timville85/4dapter/Product Images/IMG_2103.jpeg

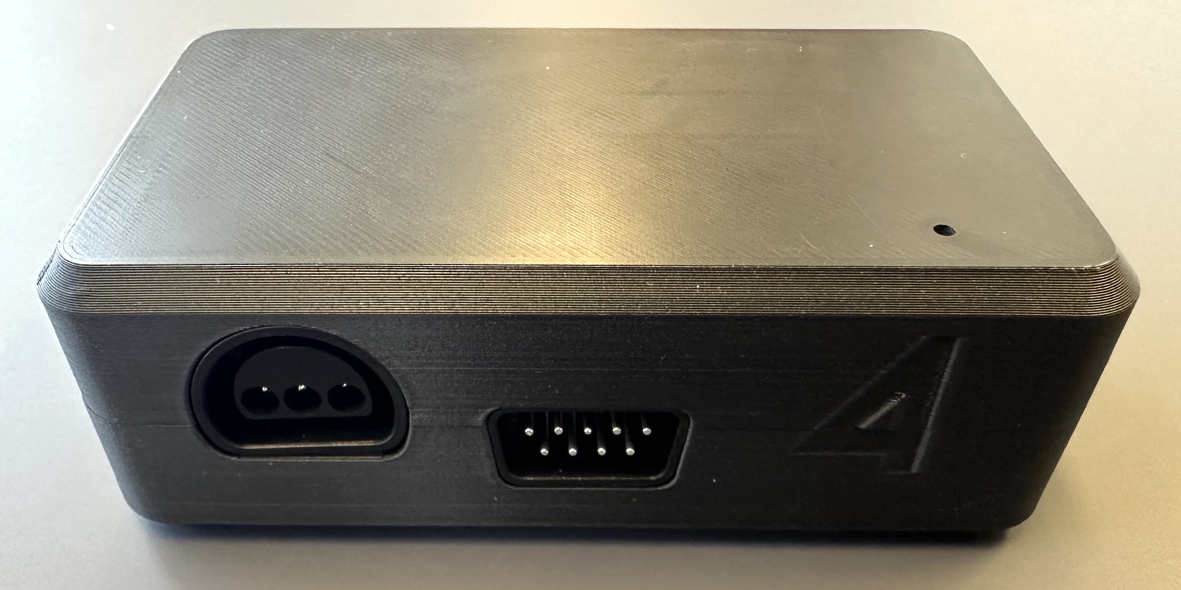
Product Images/IMG_2103.jpeg
