timville85/4dapter/Product Images/IMG_2104.jpeg

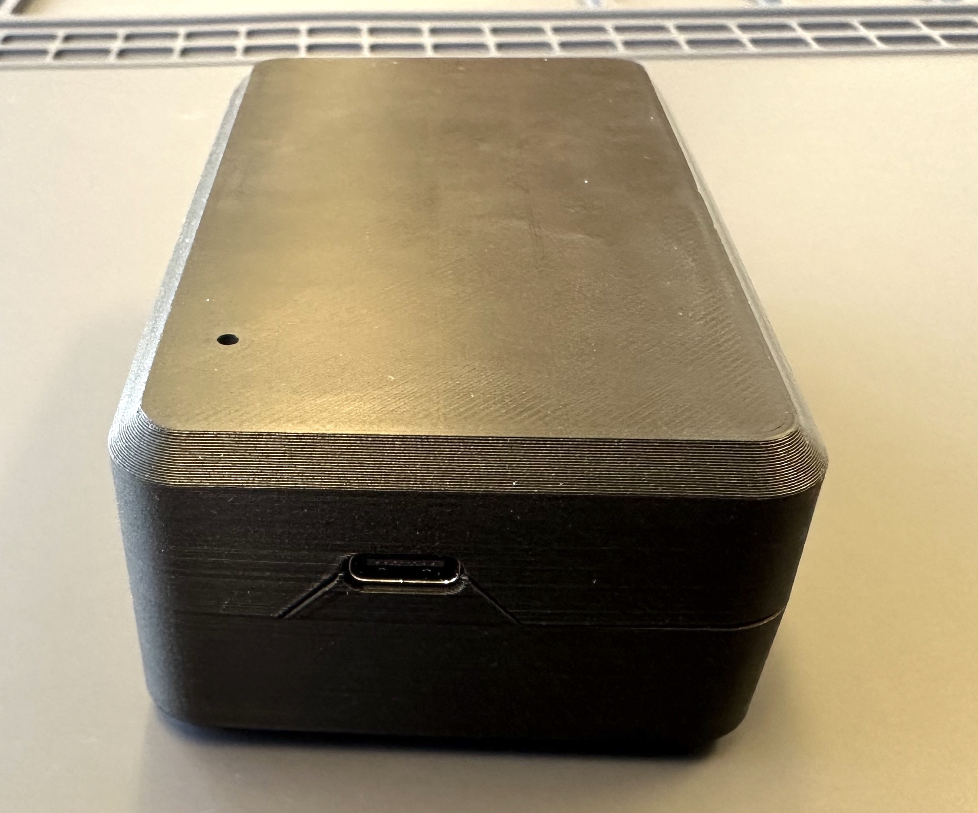
Product Images/IMG_2104.jpeg
