timville85/4dapter/Product Images/IMG_2105.jpeg

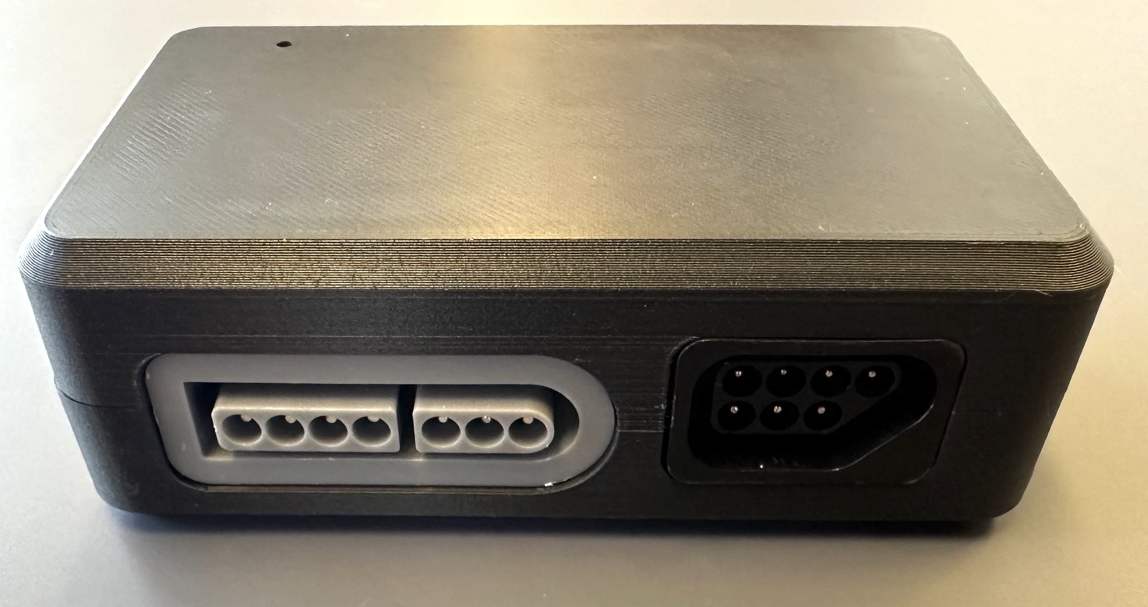
Product Images/IMG_2105.jpeg
