timville85/4dapter/Product Images/IMG_2106.jpeg

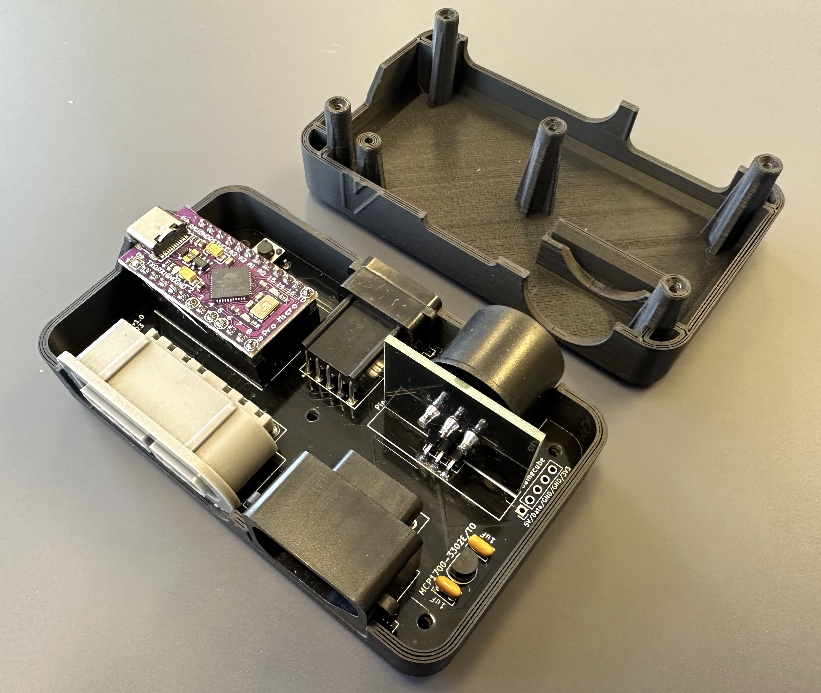
Product Images/IMG_2106.jpeg
