timville85/4dapter/Product Images/IMG_2107.jpeg

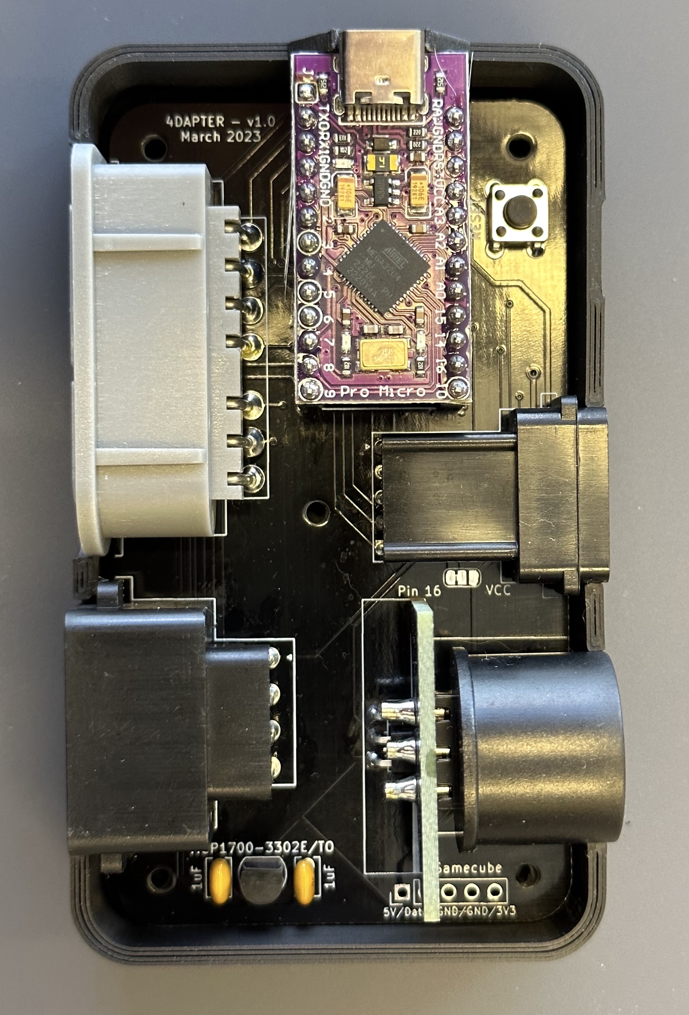
Product Images/IMG_2107.jpeg
