timville85/4dapter/Product Images/IMG_2108.jpeg

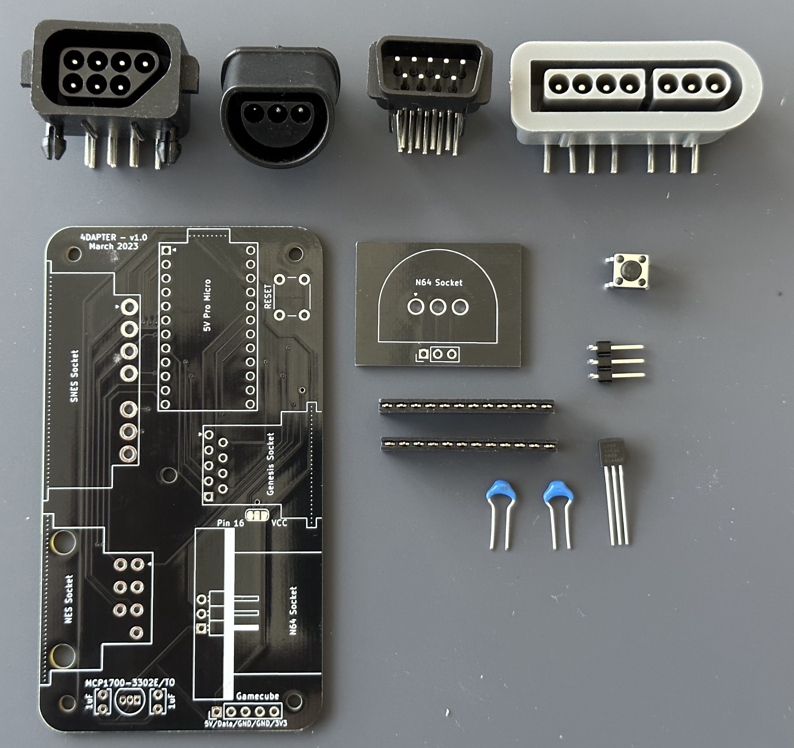
Product Images/IMG_2108.jpeg
