timville85/4dapter/Product Images/IMG_2116.jpg

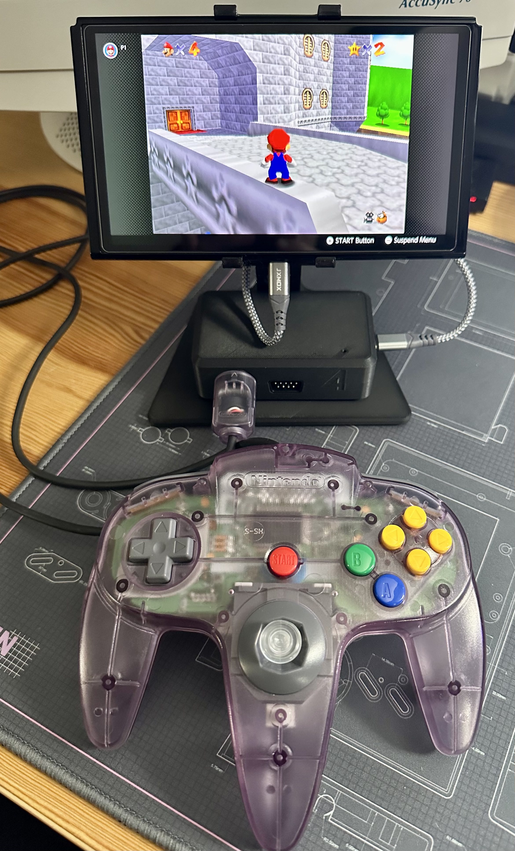
Product Images/IMG_2116.jpg
