timville85/4dapter/Product Images/IMG_2120.jpg

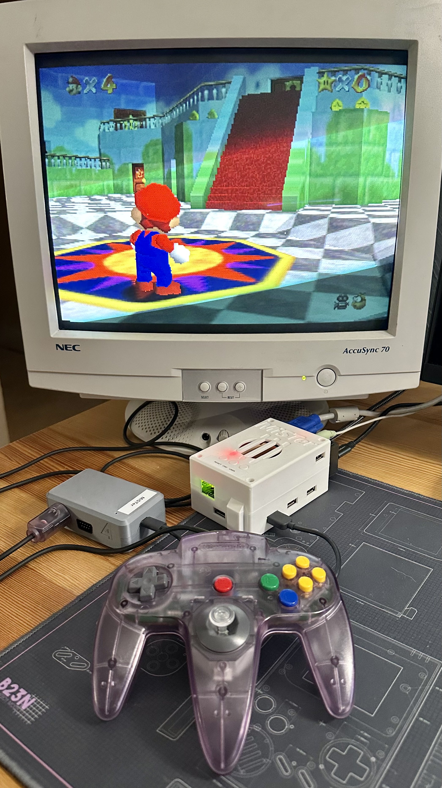
Product Images/IMG_2120.jpg
