timville85/4dapter/4dapter_FW-4P-HID/Gamepad.cpp

/*
 * Gamepad.cpp — USB HID gamepad implementation for 4dapter
 *
 * Copyright (C) 2026 4dapter project
 *
 * Original HID/PluggableUSB gamepad approach from NicoHood/HID (2014–2015);
 * later adaptations by Mikael Norrgård (2020). This version modified for 4dapter.
 *
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
 * You should have received a copy of the GNU General Public License
 * along with this program.  If not, see <https://www.gnu.org/licenses/>.
 */
#include "Gamepad.h"

static const uint8_t _hidReportDescriptor[] PROGMEM = {
 0x05, 0x01, // USAGE_PAGE (Generic Desktop)
 0x09, 0x05, // USAGE (Game Pad) — 0x05 so browsers/Gamepad API recognize it; 0x04 Joystick often ignored
 0xa1, 0x01, // COLLECTION (Application)
 0xa1, 0x00, // COLLECTION (Physical)

 0x05, 0x09, // USAGE_PAGE (Button)
 0x19, 0x01, // USAGE_MINIMUM (Button 1)
 0x29, 0x18, // USAGE_MAXIMUM (Button 24)
 0x15, 0x00, // LOGICAL_MINIMUM (0)
 0x25, 0x01, // LOGICAL_MAXIMUM (1)

 0x95, 0x18, // REPORT_COUNT (24)
 0x75, 0x01, // REPORT_SIZE (1)
 0x81, 0x02, // INPUT (Data,Var,Abs)

 0x05, 0x01, // USAGE_PAGE (Generic Desktop)
 0x09, 0x01, // USAGE (pointer)
 0xa1, 0x00, // COLLECTION (Physical)
 0x09, 0x30, // USAGE (X)
 0x09, 0x31, // USAGE (Y)
 0x15, 0x80, /* LOGICAL_MINIMUM (-128) */
 0x25, 0x7F, /* LOGICAL_MAXIMUM (127) */
 0x95, 0x02, // REPORT_COUNT (2)
 0x75, 0x08, // REPORT_SIZE (8)
 0x81, 0x02, // INPUT (Data,Var,Abs)
 0xc0, // END_COLLECTION

 0xc0, // END_COLLECTION
 0xc0, // END_COLLECTION
};

Gamepad_::Gamepad_(void) : PluggableUSBModule(1, 1, epType), protocol(HID_REPORT_PROTOCOL), idle(1), _plugged(false)
{
  epType[0] = EP_TYPE_INTERRUPT_IN;
  _plugged = PluggableUSB().plug(this);
}

int Gamepad_::getInterface(uint8_t* interfaceCount)
{
  *interfaceCount += 1;
  HIDDescriptor hidInterface = {
    D_INTERFACE(pluggedInterface, 1, USB_DEVICE_CLASS_HUMAN_INTERFACE, HID_SUBCLASS_NONE, HID_PROTOCOL_NONE),
    D_HIDREPORT(sizeof(_hidReportDescriptor)),
    D_ENDPOINT(USB_ENDPOINT_IN(pluggedEndpoint), USB_ENDPOINT_TYPE_INTERRUPT, USB_EP_SIZE, 0x01)
  };
  return USB_SendControl(0, &hidInterface, sizeof(hidInterface));
}

int Gamepad_::getDescriptor(USBSetup& setup)
{
  if (setup.bmRequestType != REQUEST_DEVICETOHOST_STANDARD_INTERFACE) return 0;
  if (setup.wValueH != HID_REPORT_DESCRIPTOR_TYPE) return 0;
  if (setup.wIndex != pluggedInterface) return 0;
  protocol = HID_REPORT_PROTOCOL;
  return USB_SendControl(TRANSFER_PGM, _hidReportDescriptor, sizeof(_hidReportDescriptor));
}

bool Gamepad_::setup(USBSetup& setup)
{
  if (pluggedInterface != setup.wIndex) return false;
  uint8_t request = setup.bRequest;
  uint8_t requestType = setup.bmRequestType;
  if (requestType == REQUEST_DEVICETOHOST_CLASS_INTERFACE)
  {
    if (request == HID_GET_REPORT) return true;
    if (request == HID_GET_PROTOCOL) return true;
  }
  if (requestType == REQUEST_HOSTTODEVICE_CLASS_INTERFACE)
  {
    if (request == HID_SET_PROTOCOL)
    {
      protocol = setup.wValueL;
      return true;
    }
    if (request == HID_SET_IDLE)
    {
      idle = setup.wValueL;
      return true;
    }
  }
  return false;
}

void Gamepad_::reset()
{
  _GamepadReport.X = 0;
  _GamepadReport.Y = 0;
  _GamepadReport.buttons = 0;
  if (_plugged) this->send();
}

void Gamepad_::send()
{
  if (_plugged)
  {
    USB_Send(pluggedEndpoint | TRANSFER_RELEASE, &_GamepadReport, sizeof(GamepadReport));
  }
}

uint8_t Gamepad_::getShortName(char* name)
{
  if (!next)
  {
    strcpy(name, usbSerialNumber);
    return strlen(name);
  }
  return 0;
}
